Matt-Pettit/SmartNest/Power Subsystem/Design schematic/Design schematic.kicad_sch

## KiCad design Power Subsystem/Design schematic/Design schematic.kicad_sch (2024-05-12)

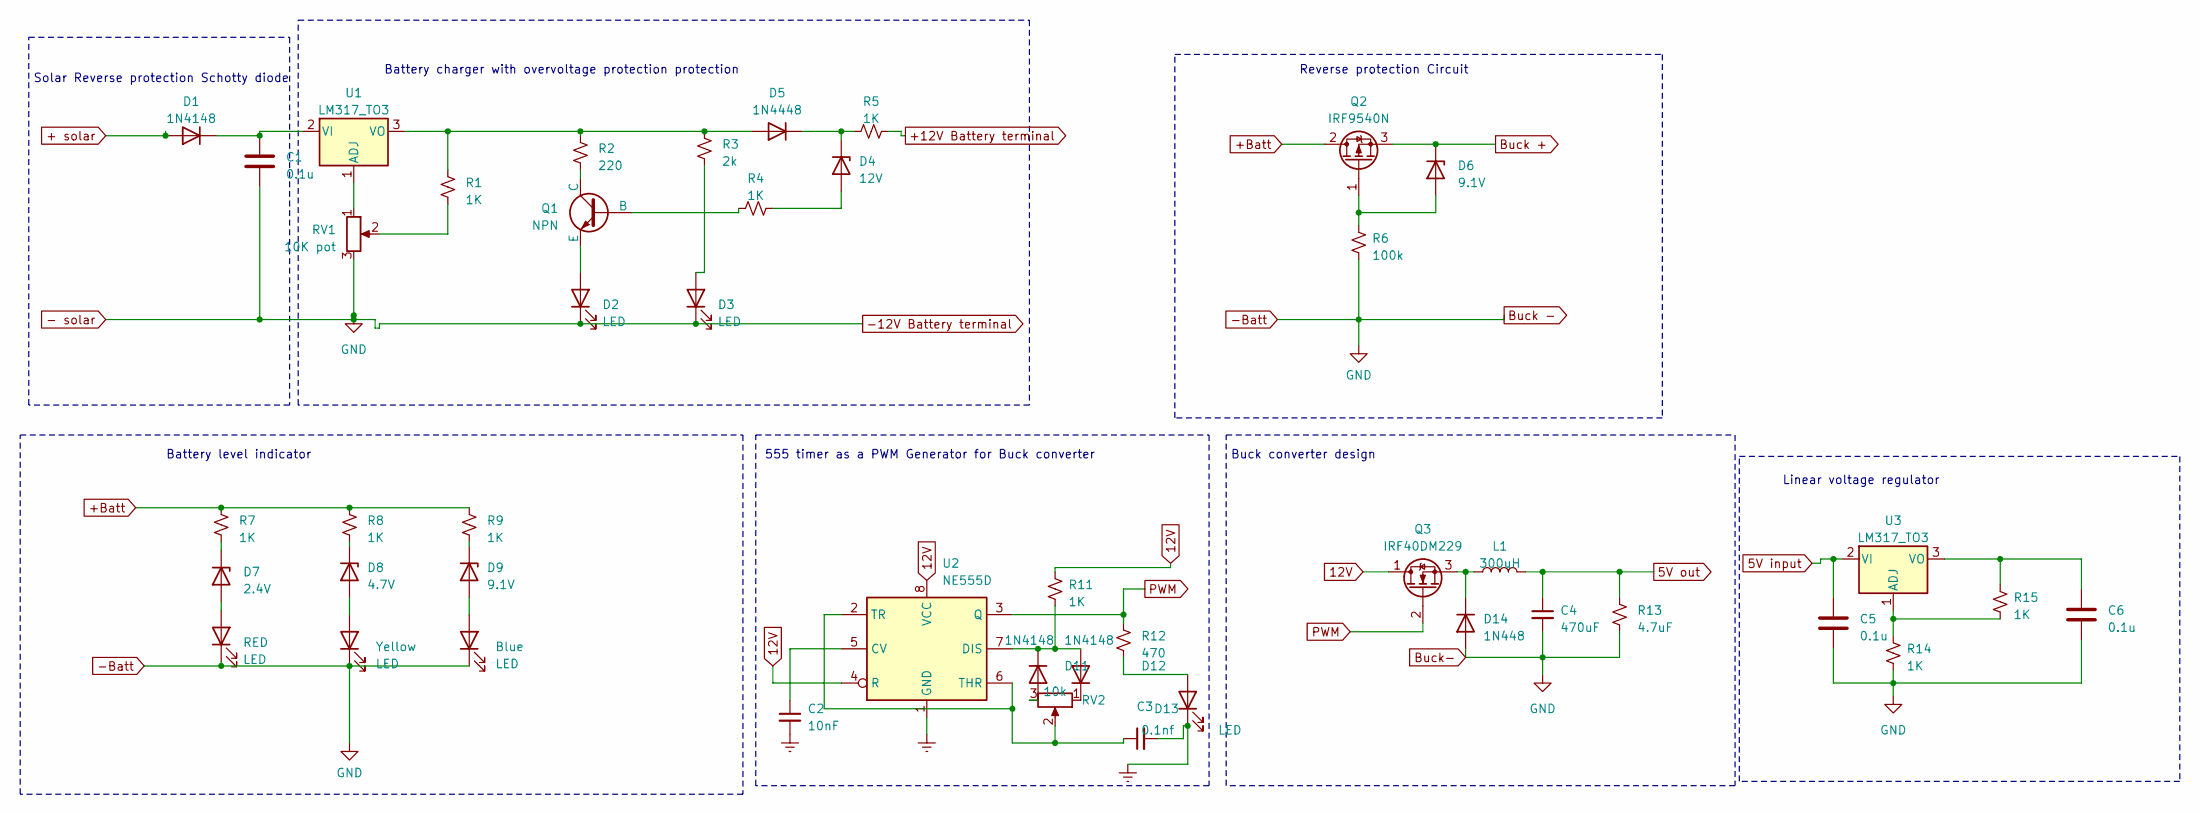
[picture p8: schematic Design schematic.kicad_sch]

Parts:
Blue: LED
C1, C5, C6: 0.1u
C2: 10nF
C3: 0.1nf
C4: 470uF
D1, D11, D12: 1N4148; D_DO-35_SOD27_P7.62mm_Horizontal
D2, D3, D13: LED
D4: 12V
D5: 1N4448; D_DO-35_SOD27_P7.62mm_Horizontal
D6, D9: 9.1V
D7: 2.4V
D8: 4.7V
D14: 1N448; D_DO-35_SOD27_P7.62mm_Horizontal
L1: 300uH
Q1: NPN
Q2: IRF9540N; TO-220-3_Vertical
Q3: IRF40DM229; DirectFET_MF
R1, R4, R5, R7, R8, R9, R11, R14, R15: 1K
R2: 220
R3: 2k
R6: 100k
R12: 470
R13: 4.7uF
RED: LED
RV1: 10K pot
RV2: 10k
U1, U3: LM317_TO3; TO-3
U2: NE555D; SOIC-8_3.9x4.9mm_P1.27mm
Yellow: LED

Connections:
5V input: C5.1, U3.2 (VI)
5V out: C4.1, L1.2, R13.2
12V: Q3.1 (D), R11.2, U2.4 (R), U2.8 (VCC)
+12V Battery terminal: R5.2
+ solar: D1.2 (A)
+Batt: Q2.2 (D), R7.1, R8.1, R9.1
- solar: Blue.1 (K), C1.2, C4.2, C5.2, C6.2, D2.1 (K), D3.1 (K), D14.2 (A), R6.1, R13.1, R14.1, RED.1 (K), RV1.3, Yellow.1 (K)
Buck +: D6.1 (K), Q2.3 (S)
Earth: C2.2, C3.2, D13.1 (K), U2.1 (GND)
unnamed: Blue.2 (A), D9.2 (A)
unnamed: C1.1, D1.1 (K), U1.2 (VI)
unnamed: C2.1, U2.5 (CV)
unnamed: C3.1, RV2.2, U2.2 (TR), U2.6 (THR)
unnamed: C6.1, R15.2, U3.3 (VO)
unnamed: D2.2 (A), Q1.3 (E)
unnamed: D3.2 (A), R3.2
unnamed: D4.1 (K), D5.1 (K), R5.1
unnamed: D4.2 (A), R4.2
unnamed: D5.2 (A), R1.1, R2.1, R3.1, U1.3 (VO)
unnamed: D6.2 (A), Q2.1 (G), R6.2
unnamed: D7.1 (K), R7.2
unnamed: D7.2 (A), RED.2 (A)
unnamed: D8.1 (K), R8.2
unnamed: D8.2 (A), Yellow.2 (A)
unnamed: D9.1 (K), R9.2
unnamed: D11.1 (K), D12.2 (A), R11.1, U2.7 (DIS)
unnamed: D11.2 (A), RV2.3
unnamed: D12.1 (K), RV2.1
unnamed: D13.2 (A), R12.2
unnamed: D14.1 (K), L1.1, Q3.3 (S)
unnamed: Q1.1 (C), R2.2
unnamed: Q1.2 (B), R4.1
unnamed: R1.2, RV1.2
unnamed: R14.2, R15.1, U3.1 (ADJ)
unnamed: RV1.1, U1.1 (ADJ)
PWM: Q3.2 (G), R12.1, U2.3 (Q)

Notes on the sheet:
Solar Reverse protection Schotty diode
Reverse protection Circuit
Buck converter design
Battery charger with overvoltage protection protection
555 timer as a PWM Generator for Buck converter
Battery level indicator
Linear voltage regulator
