Matt-Pettit/SmartNest/Power Subsystem/Design schematic/Powermodule2024.kicad_sch

## KiCad design Power Subsystem/Design schematic/Powermodule2024.kicad_sch (2024-05-12)

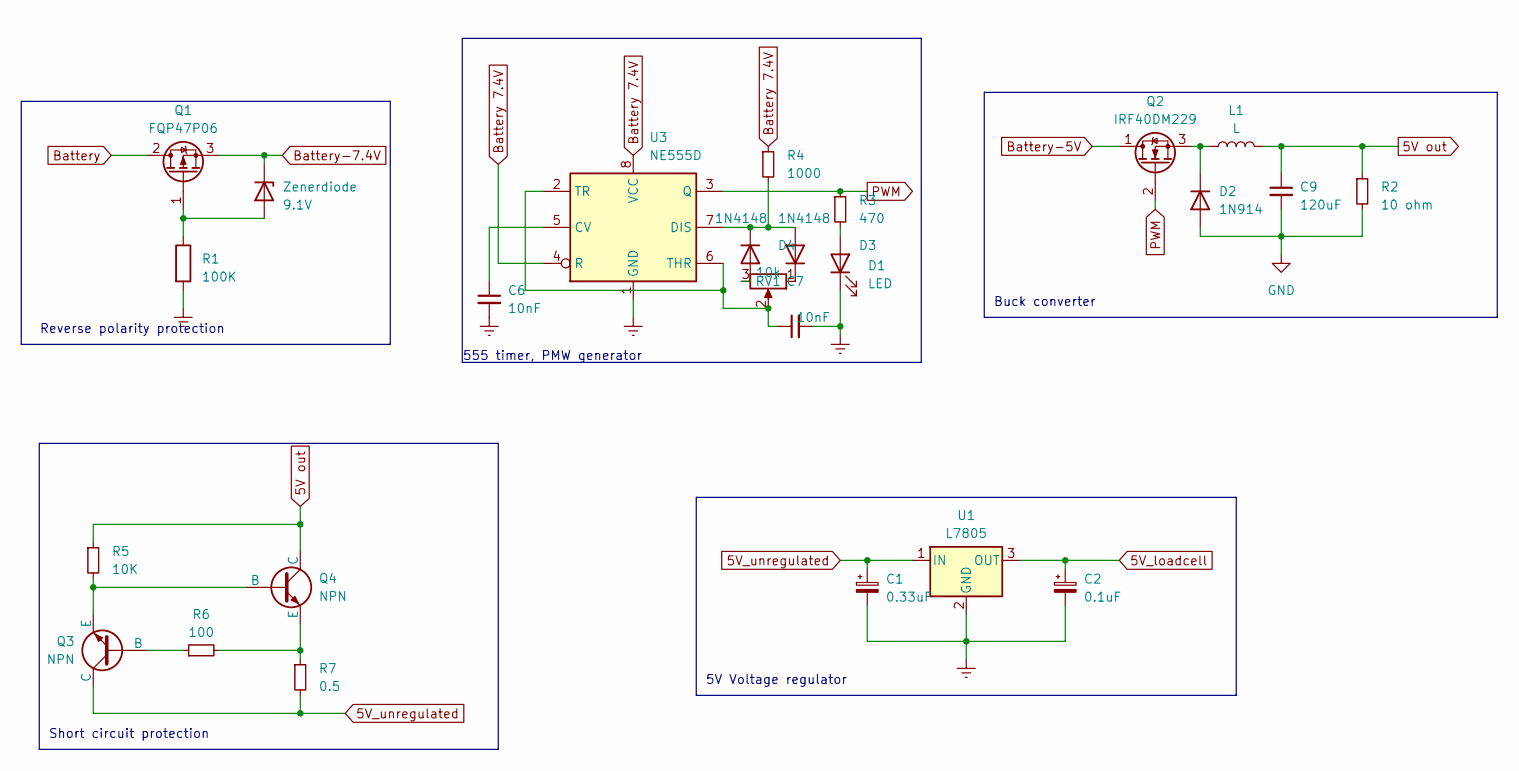
[picture p9: schematic Powermodule2024.kicad_sch]

Parts:
C1: 0.33uF
C2: 0.1uF
C6, C7: 10nF
C9: 120uF
D1: LED
D2: 1N914; D_DO-35_SOD27_P7.62mm_Horizontal
D3, D4: 1N4148; D_DO-35_SOD27_P7.62mm_Horizontal
L1: L
Q1: FQP47P06; TO-220-3_Vertical
Q2: IRF40DM229; DirectFET_MF
Q3, Q4: NPN
R1: 100K
R2: 10 ohm
R3: 470
R4: 1000
R5: 10K
R6: 100
R7: 0.5
RV1: 10k
U1: L7805
U3: NE555D; SOIC-8_3.9x4.9mm_P1.27mm
Zenerdiode: 9.1V

Connections:
5V out: C9.1, L1.2, Q4.1 (C), R2.1, R5.1
5V_loadcell: C2.1, U1.3 (OUT)
5V_unregulated: C1.1, Q3.1 (C), R7.2, U1.1 (IN)
Battery: Q1.2 (D)
Battery 7.4V: R4.1, U3.4 (R), U3.8 (VCC)
Battery-5V: Q2.1 (D)
Battery-7.4V: Q1.3 (S), Zenerdiode.1 (K)
Earth: C1.2, C2.2, C6.2, C7.2, D1.1 (K), R1.2, U1.2 (GND), U3.1 (GND)
GND: C9.2, D2.2 (A), R2.2
unnamed: C6.1, U3.5 (CV)
unnamed: C7.1, RV1.2, U3.2 (TR), U3.6 (THR)
unnamed: D1.2 (A), R3.2
unnamed: D2.1 (K), L1.1, Q2.3 (S)
unnamed: D3.1 (K), RV1.1
unnamed: D3.2 (A), D4.1 (K), R4.2, U3.7 (DIS)
unnamed: D4.2 (A), RV1.3
unnamed: Q1.1 (G), R1.1, Zenerdiode.2 (A)
unnamed: Q3.2 (B), R6.1
unnamed: Q3.3 (E), Q4.2 (B), R5.2
unnamed: Q4.3 (E), R6.2, R7.1
PWM: Q2.2 (G), R3.1, U3.3 (Q)

Notes on the sheet:
5V Voltage regulator
Short circuit protection
555 timer, PMW generator
Buck converter
Reverse polarity protection
